ajayre/r107-ac-controller/Electronics/Datasheets/Arduino-Nano-pinout.jpg

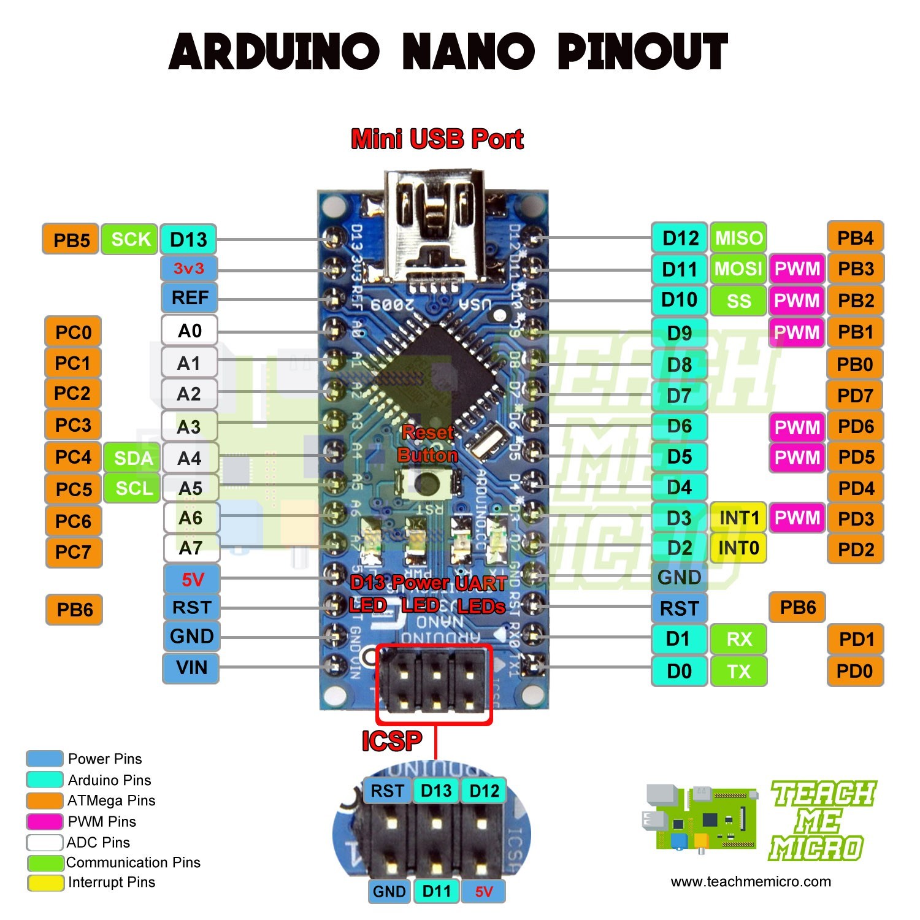
Electronics/Datasheets/Arduino-Nano-pinout.jpg
