ajayre/r107-ac-controller/Electronics/Datasheets/feather_schem.png

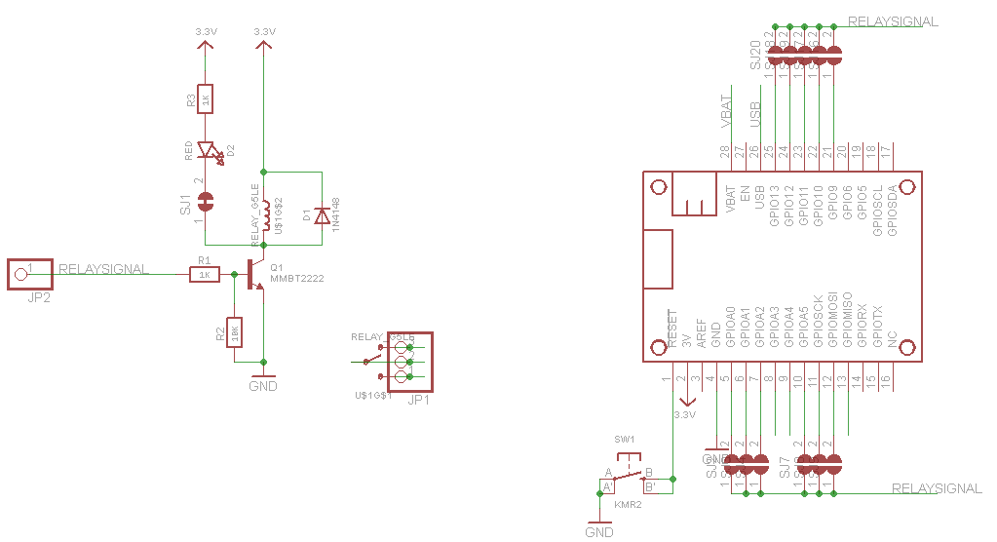
Electronics/Datasheets/feather_schem.png
