ajayre/r107-ac-controller/Electronics/PCB/R107 AC Controller/R107 AC Controller Board Render.png

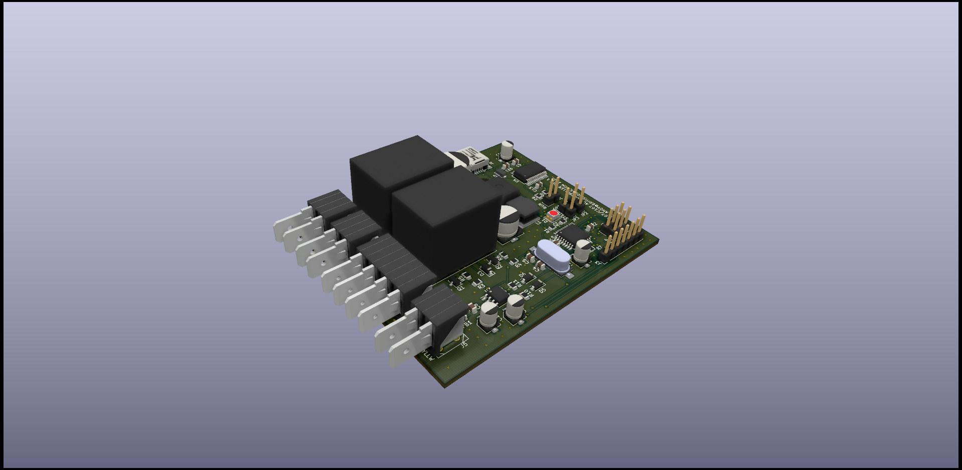
Electronics/PCB/R107 AC Controller/R107 AC Controller Board Render.png
