ajayre/r107-ac-controller/Electronics/Control Knob/Assembled.jpg

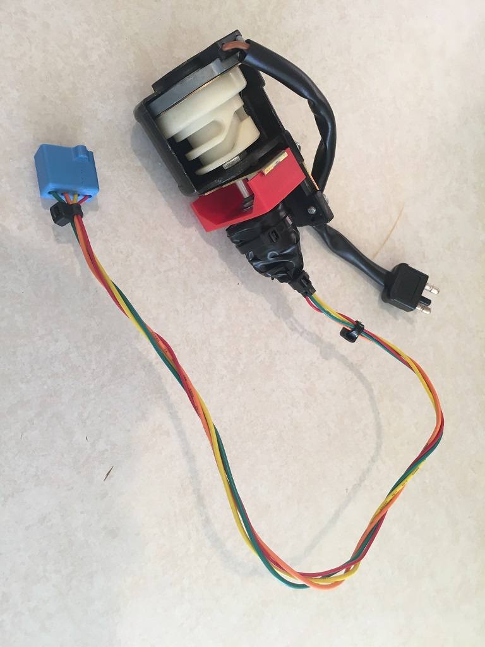
Electronics/Control Knob/Assembled.jpg
