ajayre/r107-ac-controller/Electronics/Control Knob/Control Knob KiCAD/Control Knob.sch

## KiCad design Electronics/Control Knob/Control Knob KiCAD/Control Knob.sch (2020-12-28)

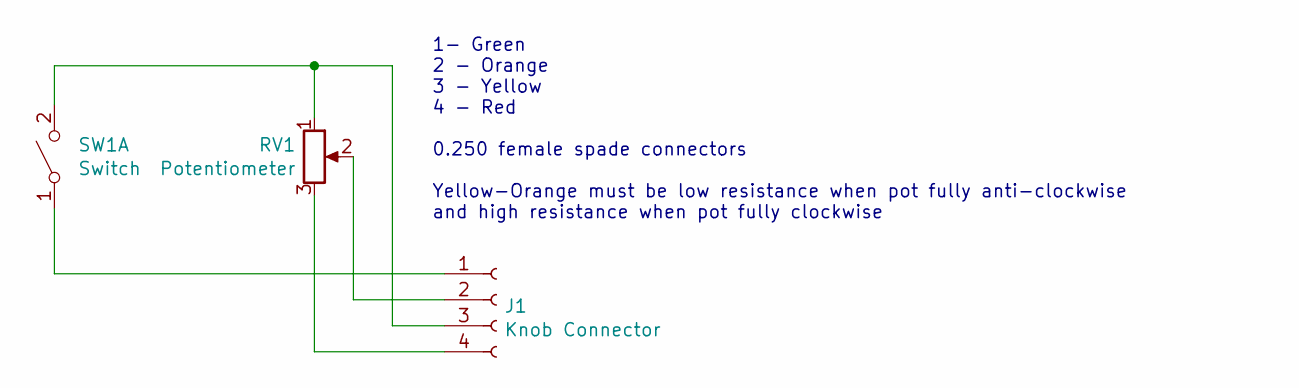
[picture p19: schematic Control Knob.sch]

Parts:
J1: Knob Connector
RV1: Potentiometer
SW1: Switch

Connections:
unnamed: J1.1, SW1.1 (A)
unnamed: J1.2, RV1.2
unnamed: J1.3, RV1.1, SW1.2 (B)
unnamed: J1.4, RV1.3

Notes on the sheet:
1- Green 2 - Orange 3 - Yellow 4 - Red 0.250 female spade connectors Yellow-Orange must be low resistance when pot fully anti-clockwise and high resistance when pot fully clockwise
